JohnSL/3DR-Simple-Delta-Printer/STL/Spiral Bed Clamp Tall.STL

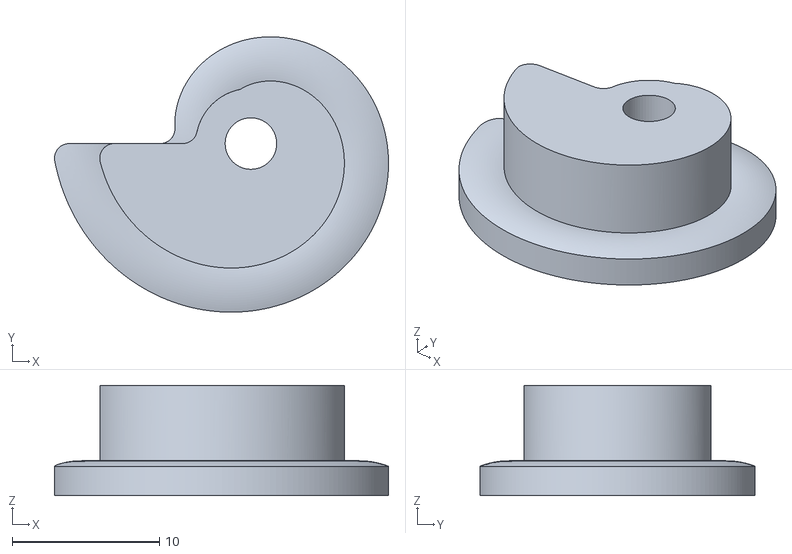
[picture p15: CAD file, 2014-05-10]
STL/Spiral Bed Clamp Tall.STL
22.7 x 18.7 x 7.50
