JohnSL/3DR-Simple-Delta-Printer/SolidWorks/FSR Platform.SLDPRT

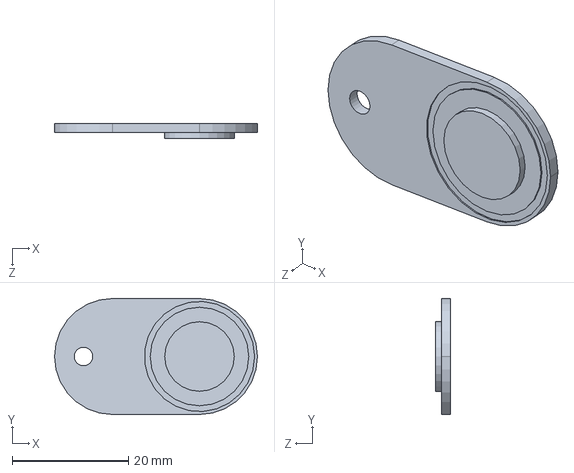
[picture p16: CAD file, 2014-05-10]
SolidWorks/FSR Platform.SLDPRT
35.0 x 20.0 x 2.50 mm
