JohnSL/3DR-Simple-Delta-Printer/STEP/Bearing Shaft Coupler.STEP

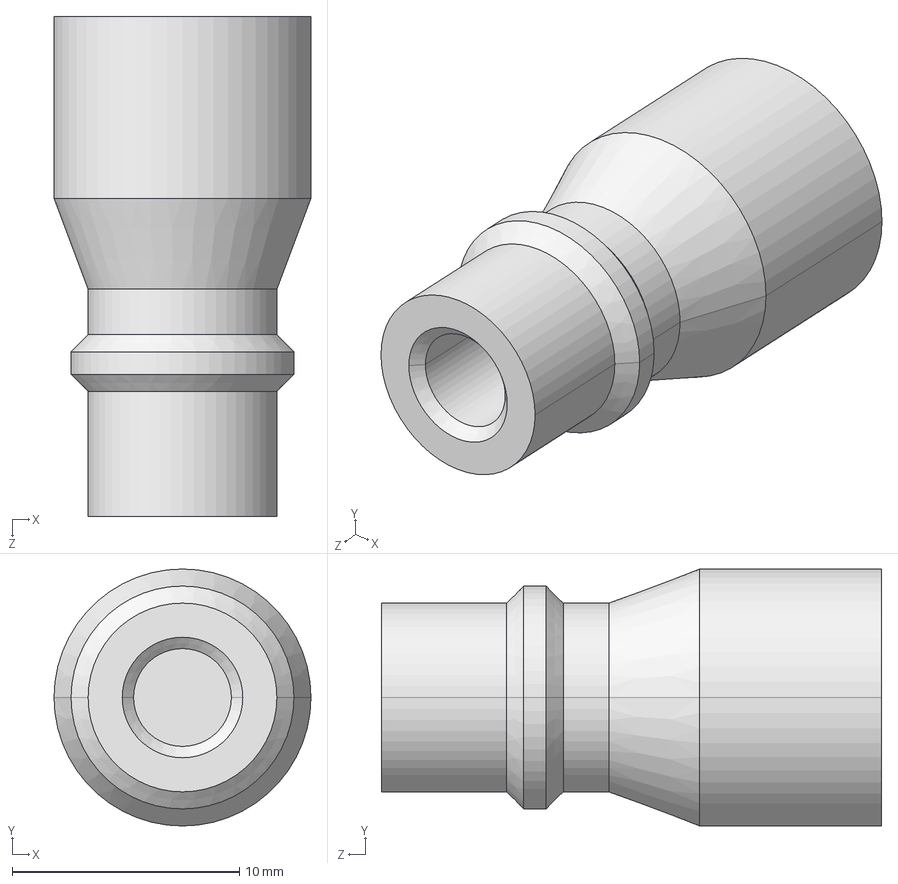
[picture p17: CAD file, 2014-02-23]
STEP/Bearing Shaft Coupler.STEP
11.3 x 11.3 x 22.0 mm
