JohnSL/3DR-Simple-Delta-Printer/STEP/Top/Wings.STEP

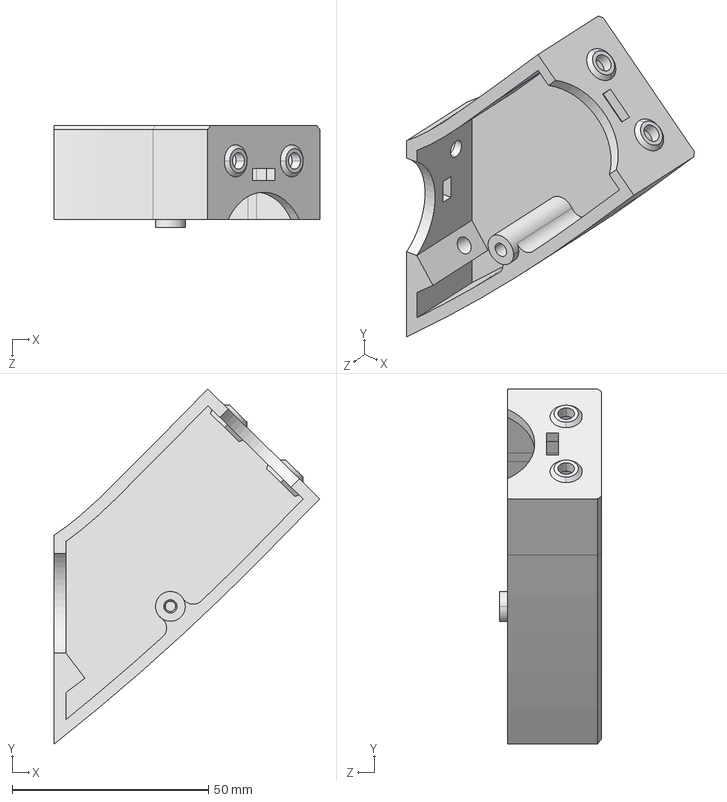
[picture p18: CAD file, 2014-03-03]
STEP/Top/Wings.STEP
67.7 x 90.5 x 26.0 mm
