JohnSL/3DR-Simple-Delta-Printer/STL/Simple Parts/Wings.STL

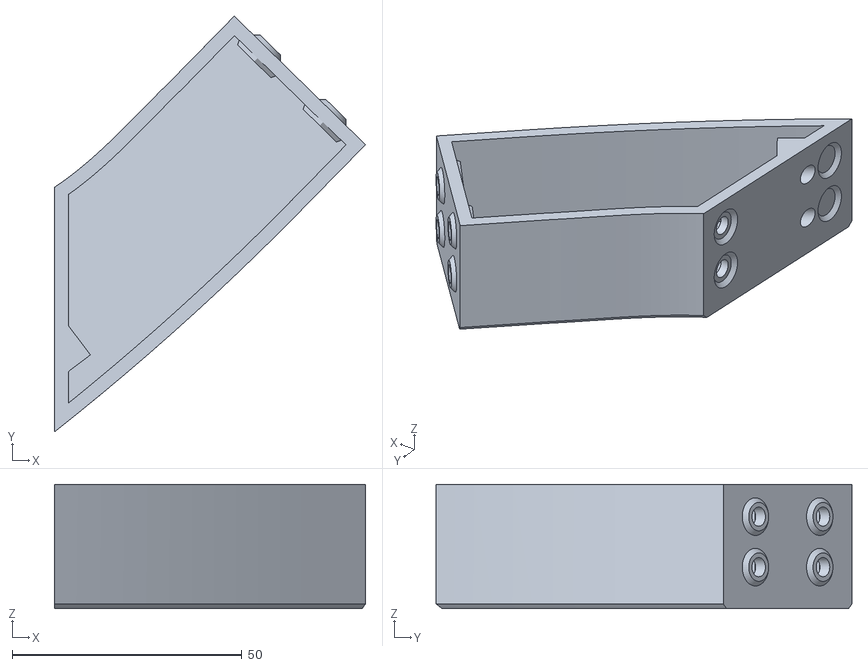
[picture p19: CAD file, 2013-11-02]
STL/Simple Parts/Wings.STL
67.7 x 90.5 x 27.0
