JohnSL/3DR-Simple-Delta-Printer/STEP/Carriage for LM8UU.STEP

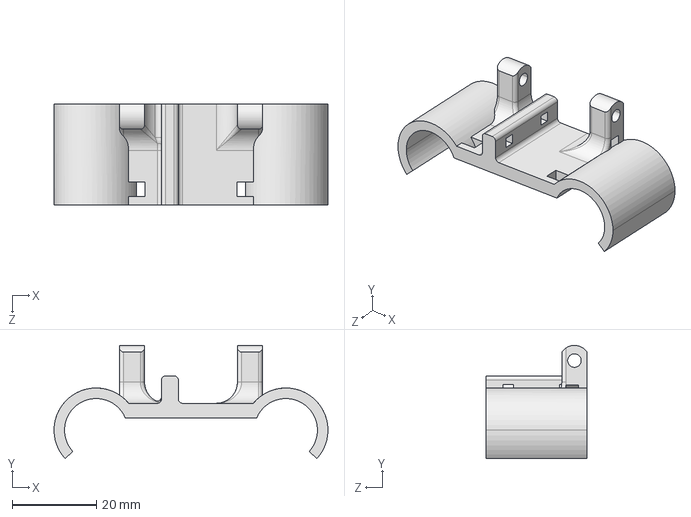
[picture p20: CAD file, 2014-02-23]
STEP/Carriage for LM8UU.STEP
65.0 x 26.9 x 24.0 mm
