JohnSL/3DR-Simple-Delta-Printer/STEP/Hot End/Hot End Holder Tabs.STEP

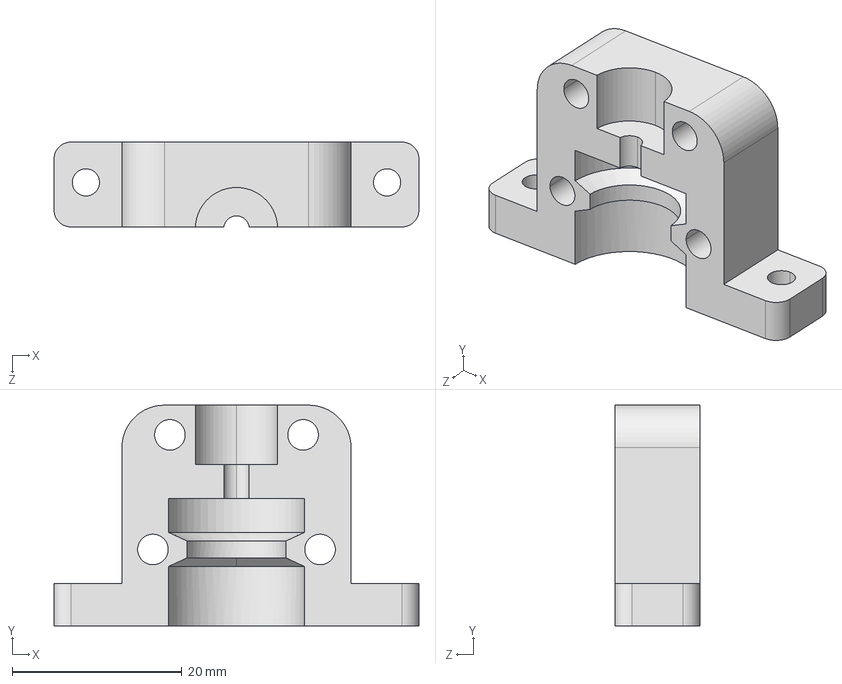
[picture p21: CAD file, 2014-02-23]
STEP/Hot End/Hot End Holder Tabs.STEP
43.0 x 26.0 x 10.0 mm
