JohnSL/3DR-Simple-Delta-Printer/STEP/Top/Wings with Power.STEP

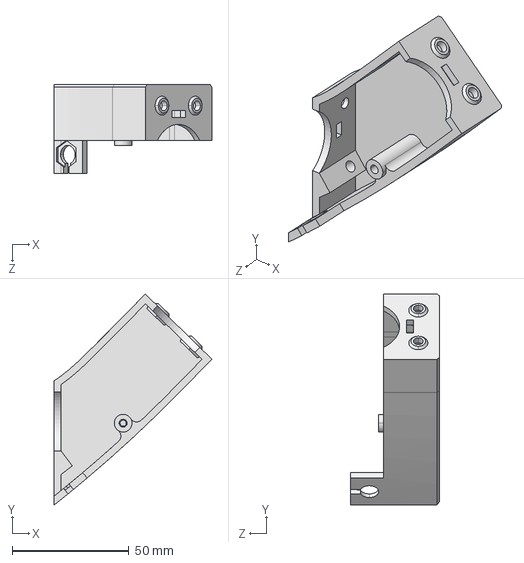
[picture p22: CAD file, 2014-03-03]
STEP/Top/Wings with Power.STEP
67.7 x 90.5 x 38.0 mm
