JohnSL/3DR-Simple-Delta-Printer/STL/2020extrusion_cap-nohole.stl

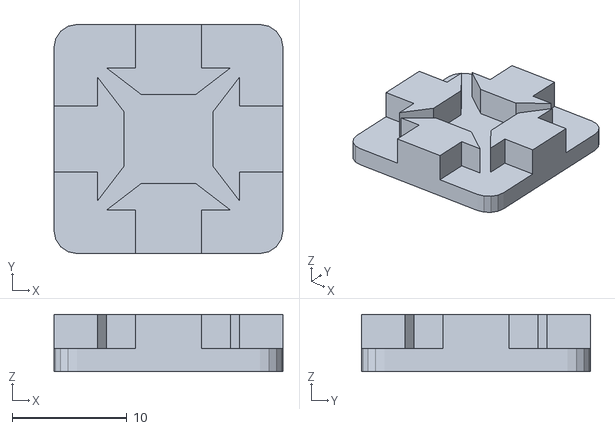
[picture p23: CAD file, 2013-11-30]
STL/2020extrusion_cap-nohole.stl
20.0 x 20.0 x 5.00
