JohnSL/3DR-Simple-Delta-Printer/STEP/Hot End/Hot End Plate.STEP

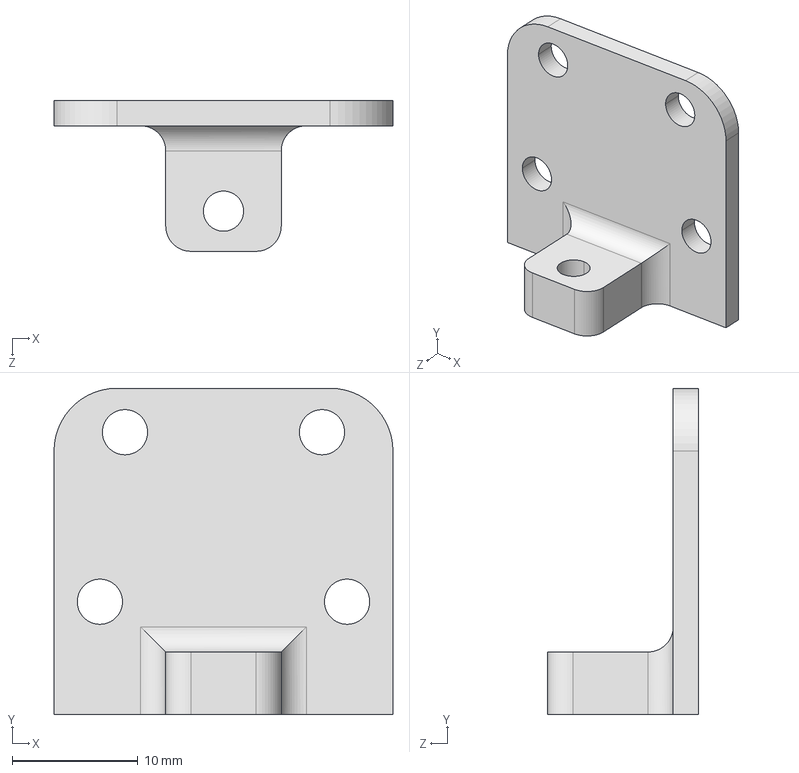
[picture p24: CAD file, 2014-02-23]
STEP/Hot End/Hot End Plate.STEP
27.0 x 26.0 x 12.0 mm
