JohnSL/3DR-Simple-Delta-Printer/STEP/Top/Wing Mirror Long Top.STEP

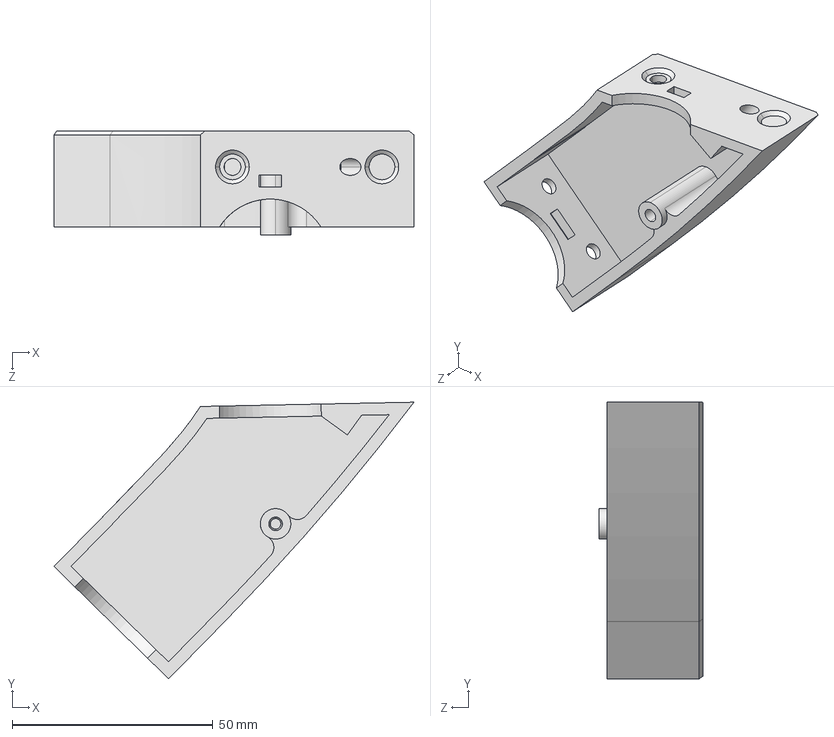
[picture p25: CAD file, 2014-03-03]
STEP/Top/Wing Mirror Long Top.STEP
89.7 x 69.0 x 26.0 mm
