JohnSL/3DR-Simple-Delta-Printer/STEP/Hot End/Fan and LED Mount.STEP

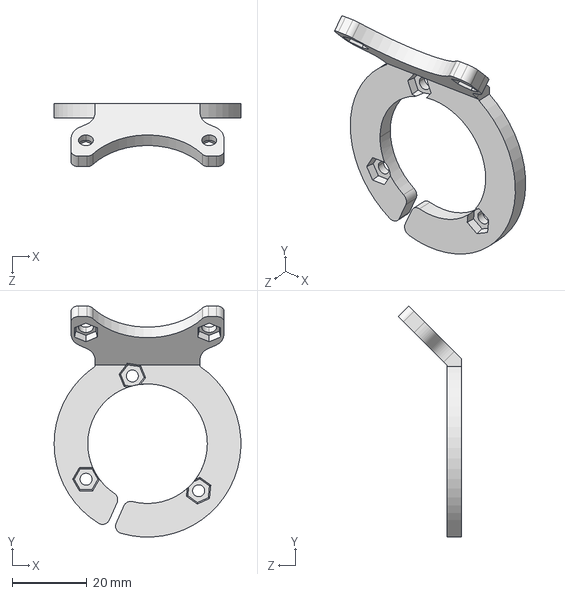
[picture p26: CAD file, 2014-02-23]
STEP/Hot End/Fan and LED Mount.STEP
50.0 x 61.8 x 17.0 mm
