JohnSL/3DR-Simple-Delta-Printer/STEP/Hot End/Platform.STEP

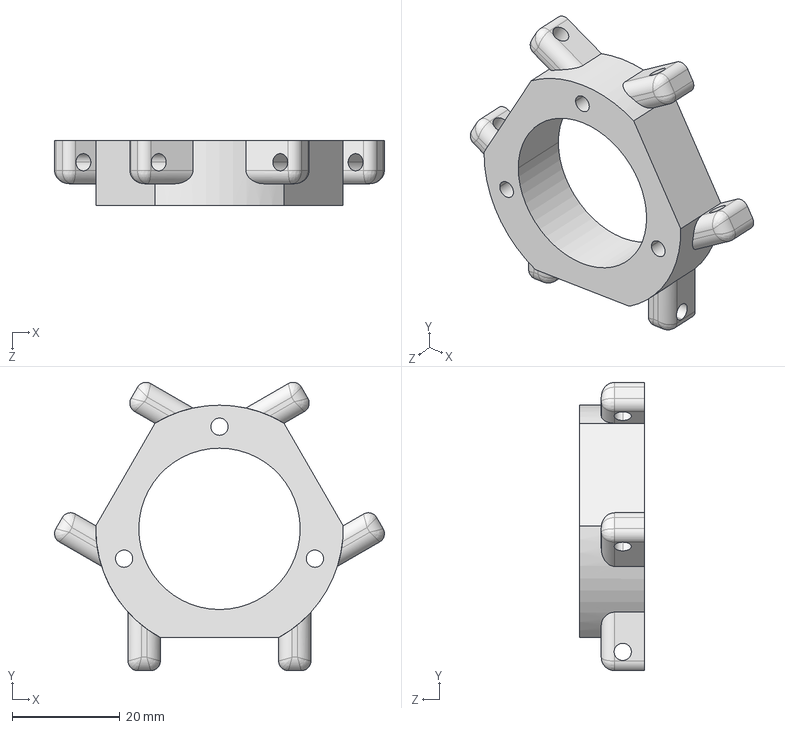
[picture p27: CAD file, 2014-02-23]
STEP/Hot End/Platform.STEP
61.4 x 53.6 x 12.0 mm
