JohnSL/3DR-Simple-Delta-Printer/SolidWorks/Rod Tensioner.SLDPRT

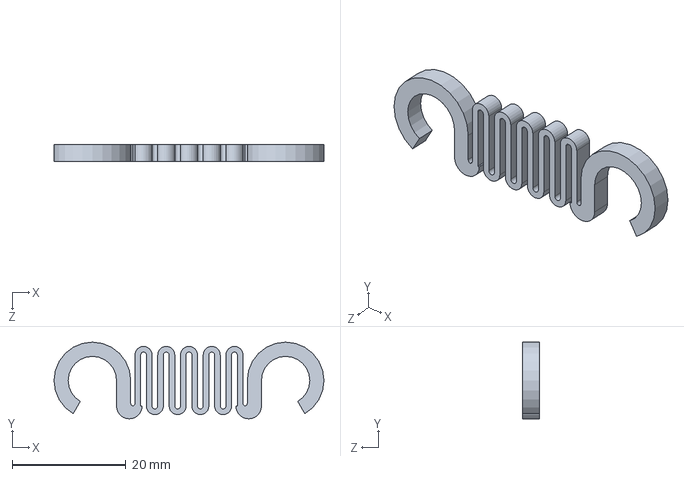
[picture p28: CAD file, 2014-01-16]
SolidWorks/Rod Tensioner.SLDPRT
47.5 x 13.5 x 3.00 mm
