JohnSL/3DR-Simple-Delta-Printer/SolidWorks/Acrylic Plate.SLDPRT

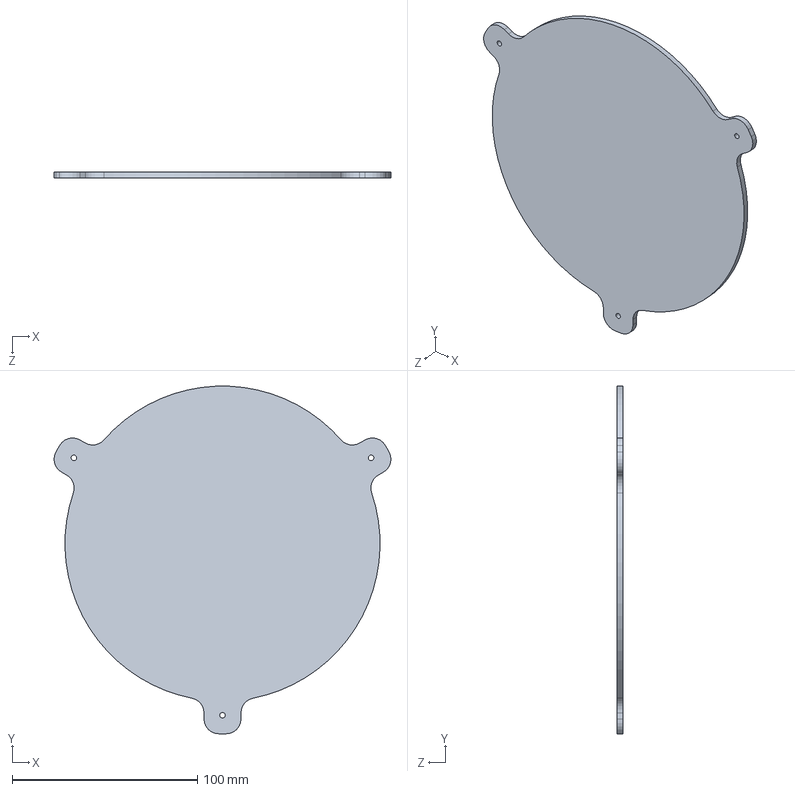
[picture p29: CAD file, 2013-11-30]
SolidWorks/Acrylic Plate.SLDPRT
181.8 x 187.5 x 3.17 mm
