JohnSL/3DR-Simple-Delta-Printer/SolidWorks/Round Plate.SLDPRT

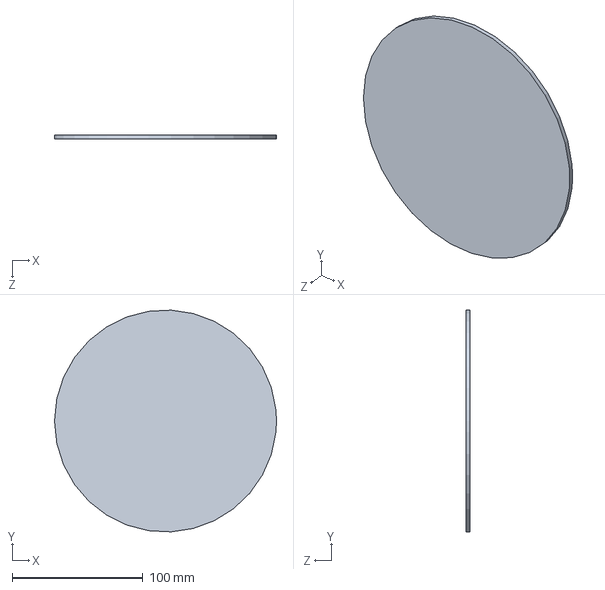
[picture p30: CAD file, 2013-11-30]
SolidWorks/Round Plate.SLDPRT
170.0 x 169.8 x 3.00 mm
