JohnSL/3DR-Simple-Delta-Printer/SolidWorks/Hot End.SLDPRT

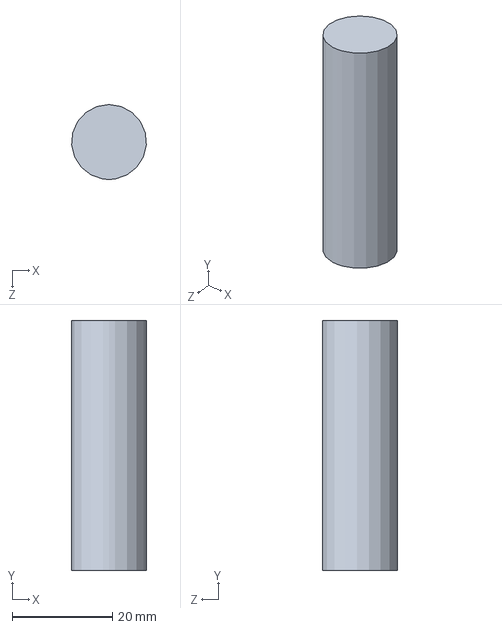
[picture p31: CAD file, 2013-11-30]
SolidWorks/Hot End.SLDPRT
14.9 x 50.0 x 15.0 mm
