JohnSL/3DR-Simple-Delta-Printer/SolidWorks/Fan.SLDPRT

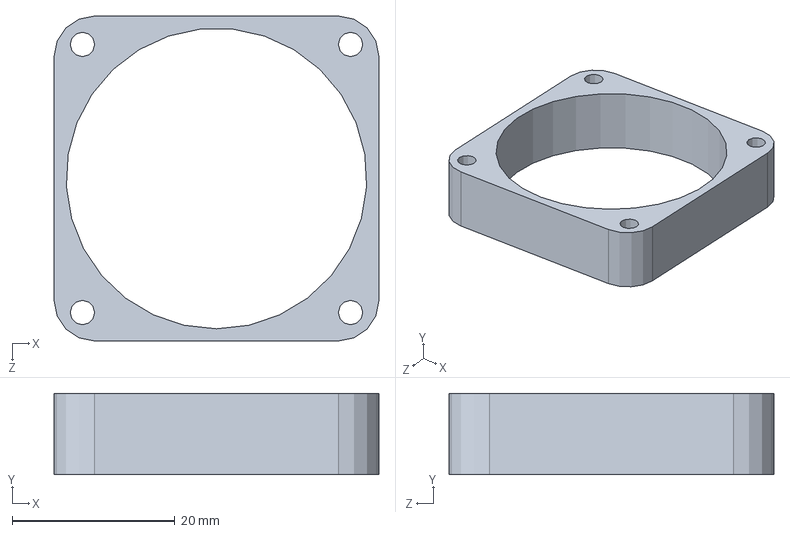
[picture p32: CAD file, 2013-11-30]
SolidWorks/Fan.SLDPRT
40.0 x 10.0 x 40.0 mm
