JohnSL/3DR-Simple-Delta-Printer/SolidWorks/Fan Side Mount.SLDPRT

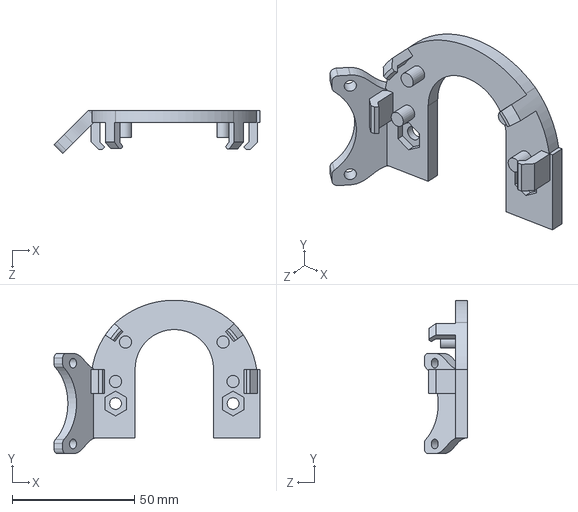
[picture p33: CAD file, 2013-11-30]
SolidWorks/Fan Side Mount.SLDPRT
84.1 x 62.7 x 17.7 mm
