JohnSL/3DR-Simple-Delta-Printer/SolidWorks/MirrorWings.SLDPRT

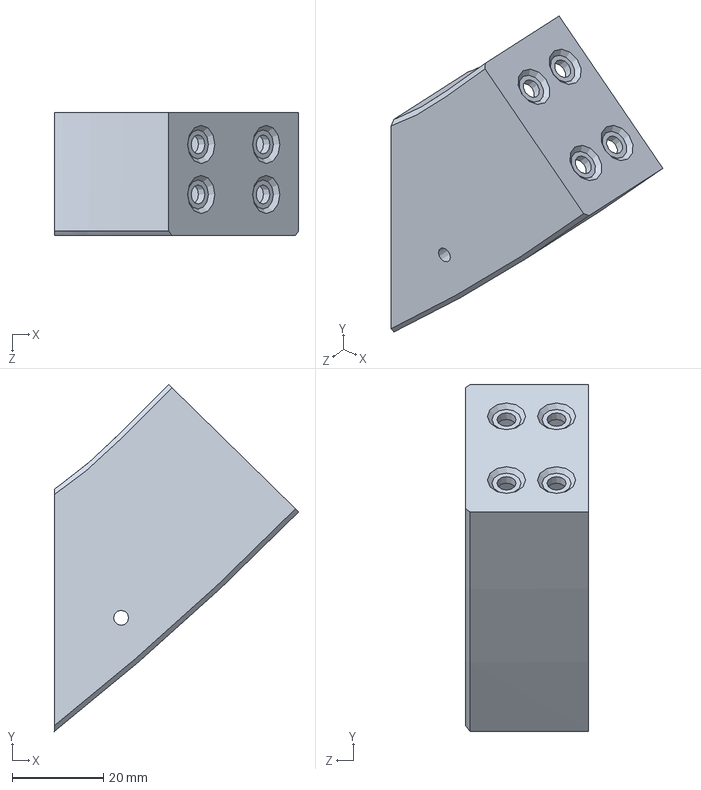
[picture p34: CAD file, 2013-11-07]
SolidWorks/MirrorWings.SLDPRT
53.7 x 76.2 x 27.0 mm
