JohnSL/3DR-Simple-Delta-Printer/SolidWorks/Spool.SLDPRT

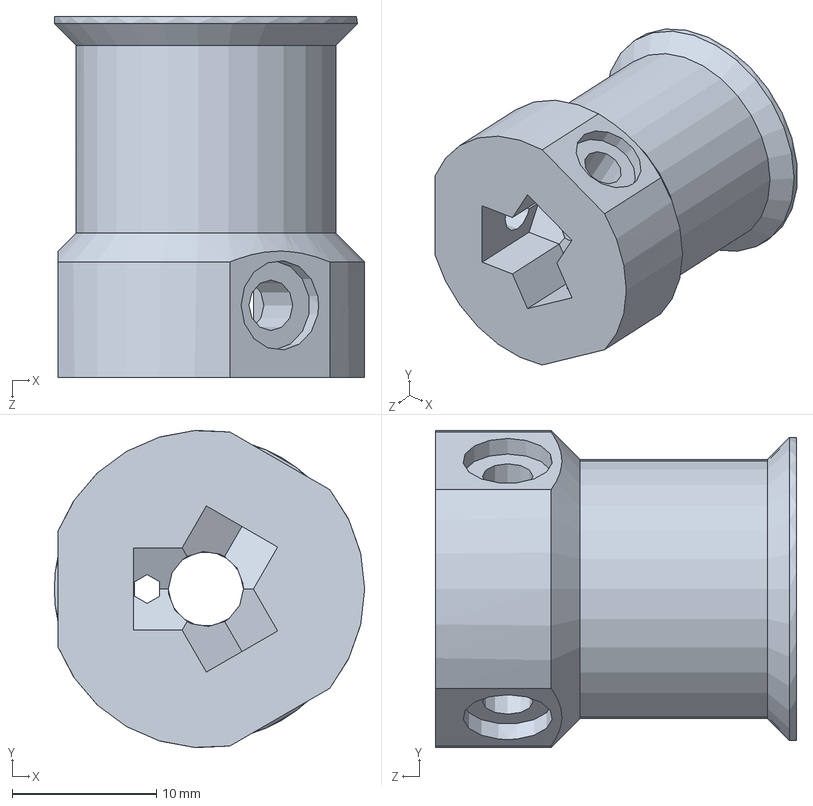
[picture p35: CAD file, 2013-11-07]
SolidWorks/Spool.SLDPRT
21.5 x 22.0 x 25.0 mm
