JohnSL/3DR-Simple-Delta-Printer/SolidWorks/Bed Holder.SLDPRT

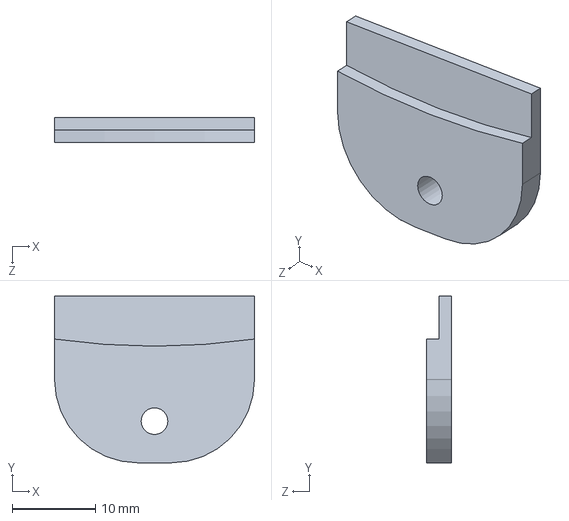
[picture p36: CAD file, 2013-10-21]
SolidWorks/Bed Holder.SLDPRT
24.0 x 20.0 x 3.00 mm
