JohnSL/3DR-Simple-Delta-Printer/SolidWorks/Wings.SLDPRT

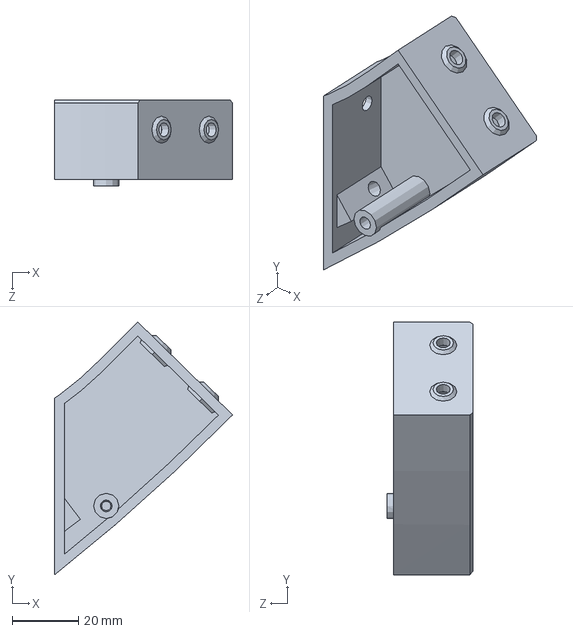
[picture p37: CAD file, 2013-10-21]
SolidWorks/Wings.SLDPRT
53.7 x 76.2 x 26.0 mm
