JohnSL/3DR-Simple-Delta-Printer/SolidWorks/3DR_Top_Electronics_Mount_V2_001_RTP.SLDPRT

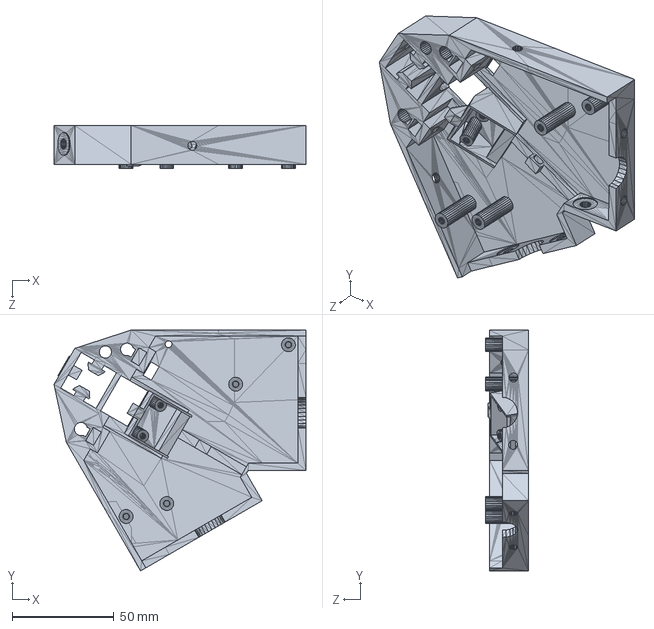
[picture p38: CAD file, 2013-10-16]
SolidWorks/3DR_Top_Electronics_Mount_V2_001_RTP.SLDPRT
123.7 x 118.2 x 21.2 mm
