JohnSL/3DR-Simple-Delta-Printer/SolidWorks/Printrboard.SLDPRT

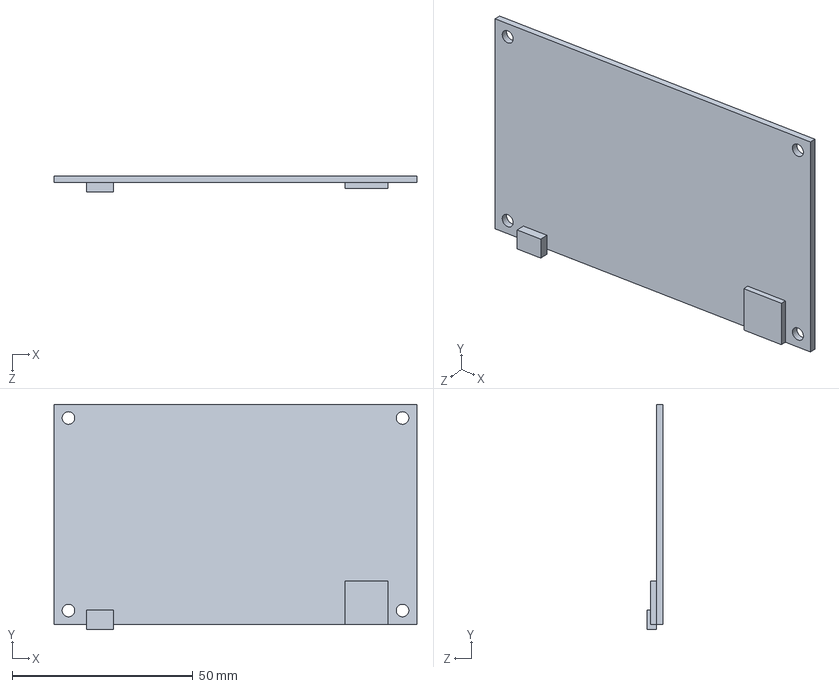
[picture p39: CAD file, 2013-10-16]
SolidWorks/Printrboard.SLDPRT
100.5 x 62.4 x 4.30 mm
