JohnSL/3DR-Simple-Delta-Printer/SolidWorks/M3 Button Head.SLDPRT

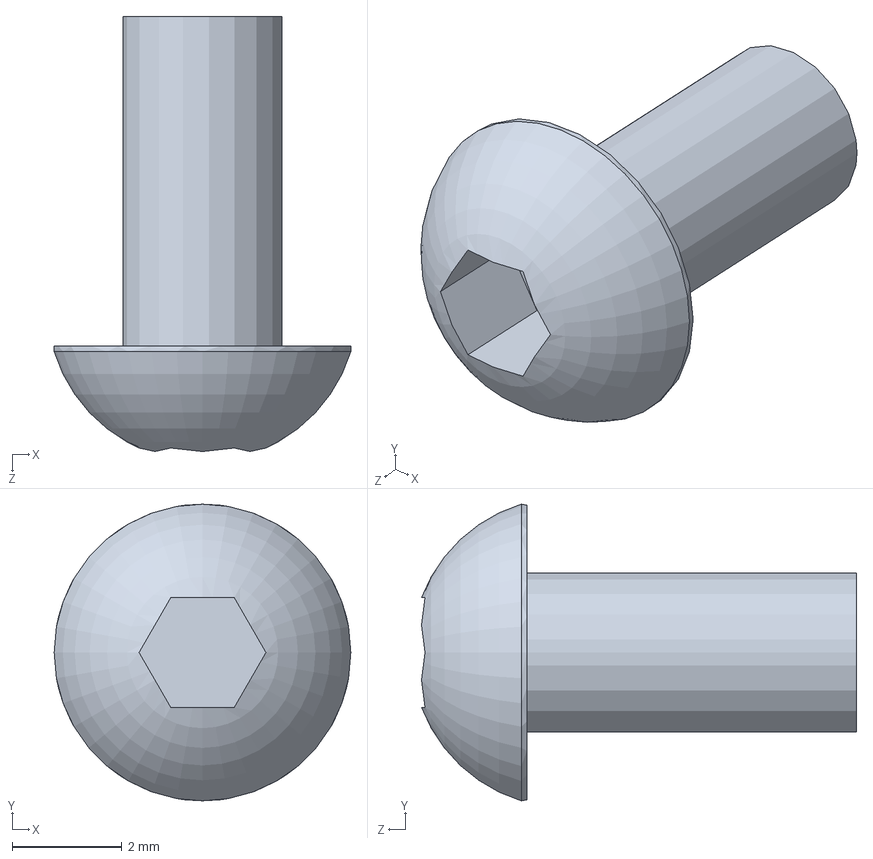
[picture p40: CAD file, 2013-10-16]
SolidWorks/M3 Button Head.SLDPRT
5.40 x 5.40 x 7.92 mm
