JohnSL/3DR-Simple-Delta-Printer/SolidWorks/3DR_Spool_V2_001_RTP.SLDPRT

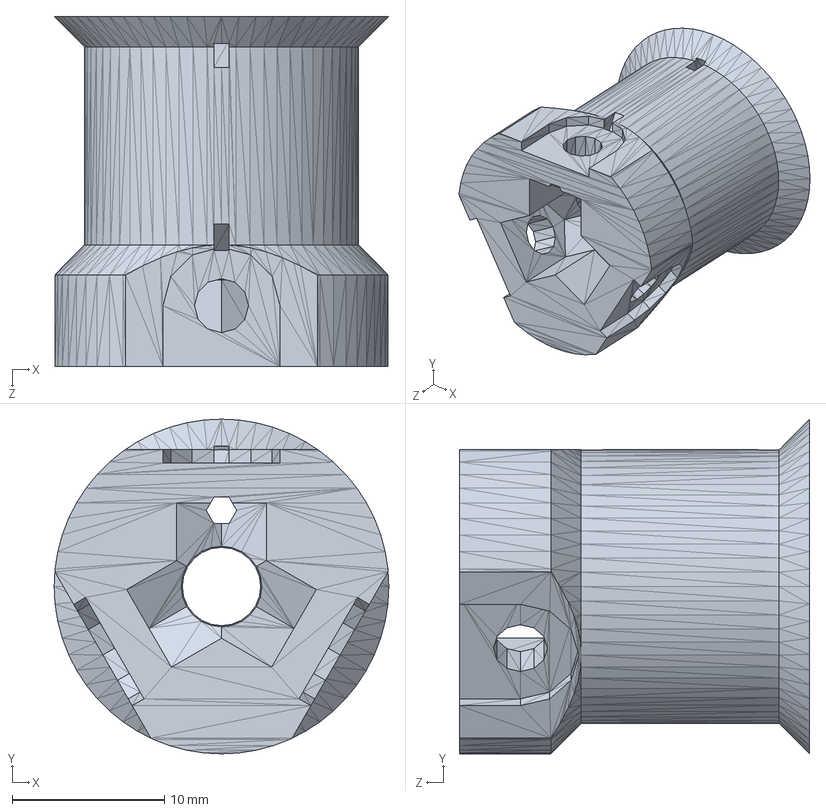
[picture p41: CAD file, 2013-10-16]
SolidWorks/3DR_Spool_V2_001_RTP.SLDPRT
22.0 x 22.0 x 23.0 mm
