JohnSL/3DR-Simple-Delta-Printer/SolidWorks/3DR_Carriage_V2_001_for_LM6UU_RTP.SLDPRT

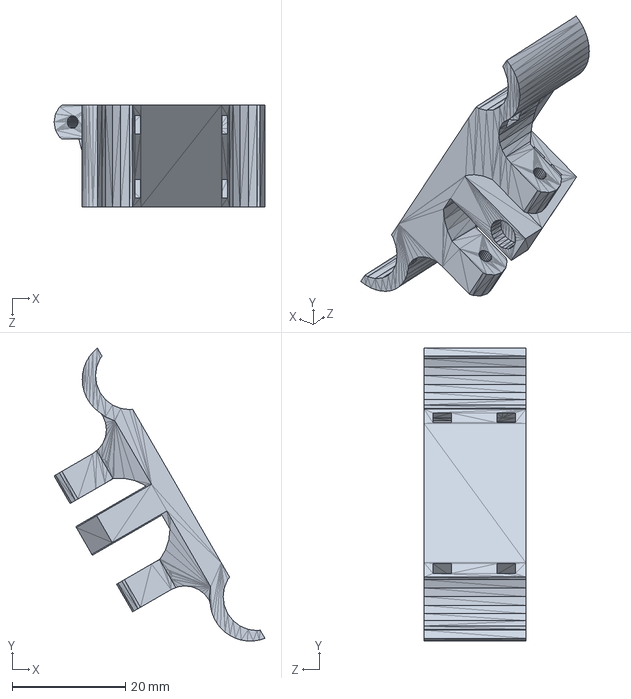
[picture p42: CAD file, 2013-10-16]
SolidWorks/3DR_Carriage_V2_001_for_LM6UU_RTP.SLDPRT
37.3 x 51.8 x 18.0 mm
