JohnSL/3DR-Simple-Delta-Printer/SolidWorks/3DR_Print_Bed_catch_V2_001_RTP.SLDPRT

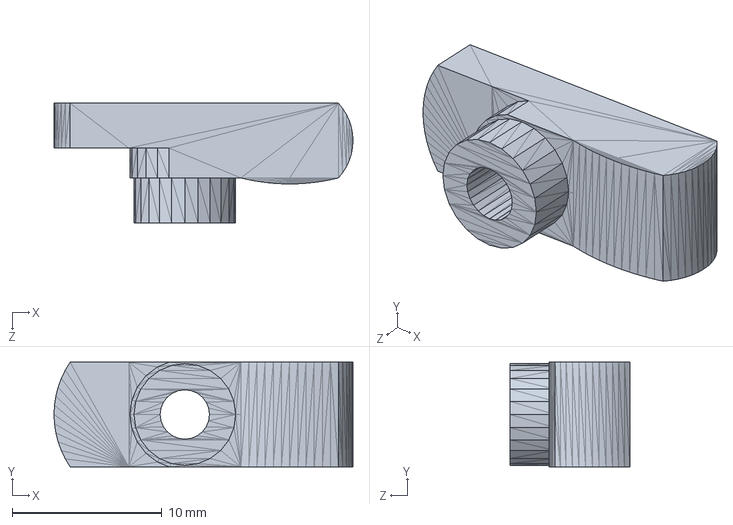
[picture p43: CAD file, 2013-10-16]
SolidWorks/3DR_Print_Bed_catch_V2_001_RTP.SLDPRT
20.0 x 7.00 x 8.00 mm
