JohnSL/3DR-Simple-Delta-Printer/SolidWorks/RGOCG8-400.SLDPRT

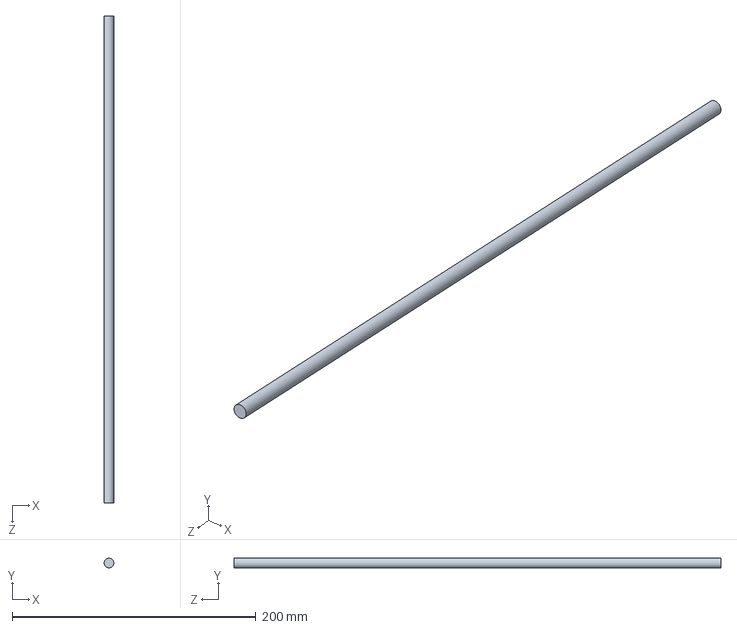
[picture p44: CAD file, 2013-10-16]
SolidWorks/RGOCG8-400.SLDPRT
8.00 x 8.00 x 400.0 mm
