JohnSL/3DR-Simple-Delta-Printer/SolidWorks/Carbon Rod.SLDPRT

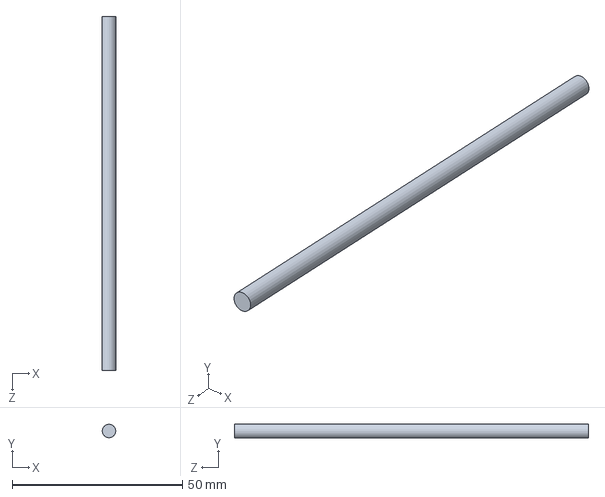
[picture p45: CAD file, 2013-10-16]
SolidWorks/Carbon Rod.SLDPRT
4.00 x 4.00 x 104.0 mm
