JohnSL/3DR-Simple-Delta-Printer/SolidWorks/3DR Bottom Center Foot.SLDPRT

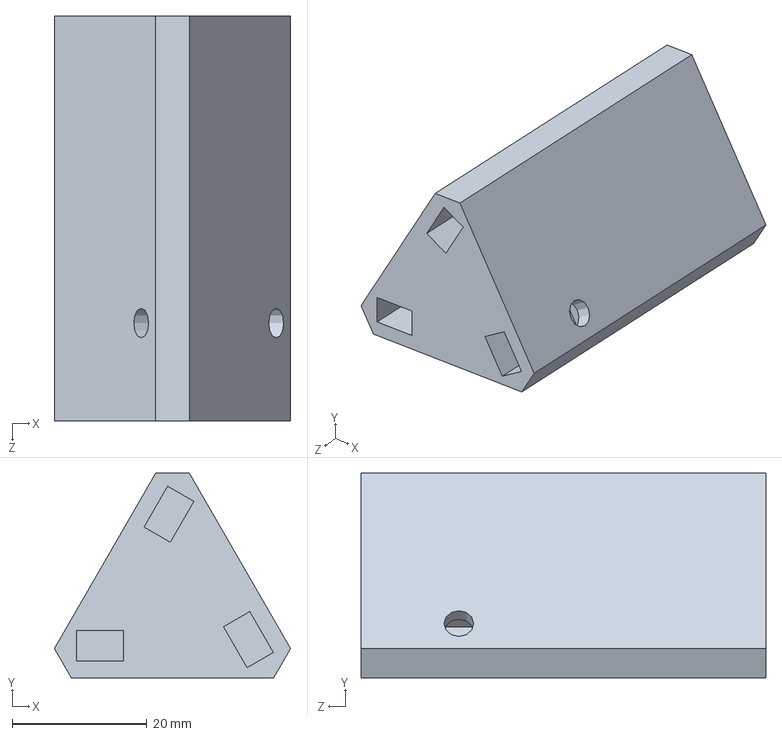
[picture p46: CAD file, 2013-10-16]
SolidWorks/3DR Bottom Center Foot.SLDPRT
35.0 x 30.3 x 60.0 mm
