JohnSL/3DR-Simple-Delta-Printer/SolidWorks/Thread.SLDPRT

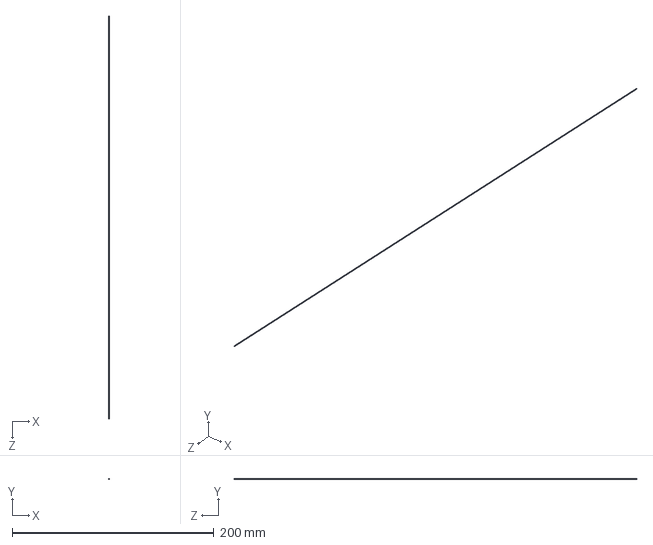
[picture p47: CAD file, 2013-10-16]
SolidWorks/Thread.SLDPRT
0.5 x 0.5 x 400.0 mm
