JohnSL/3DR-Simple-Delta-Printer/SolidWorks/Rod Ends.SLDPRT

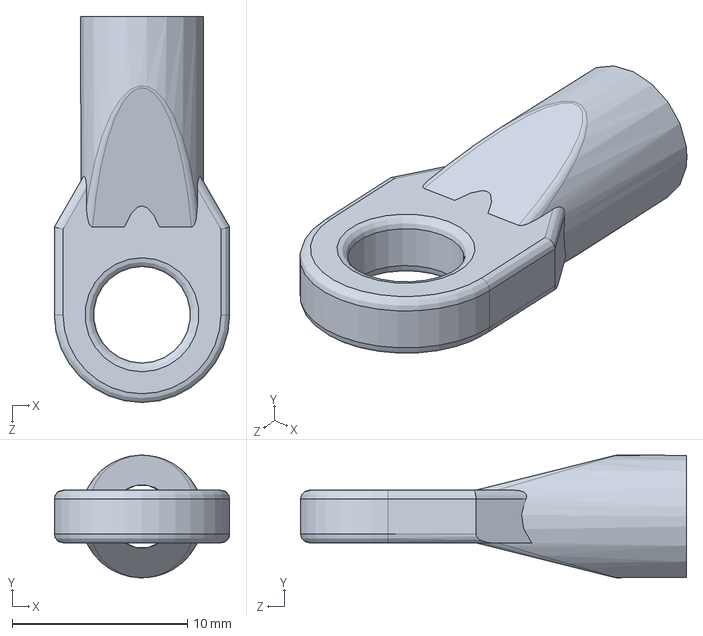
[picture p48: CAD file, 2013-10-16]
SolidWorks/Rod Ends.SLDPRT
10.0 x 6.99 x 22.0 mm
