JohnSL/3DR-Simple-Delta-Printer/SolidWorks/Carbon Rod Jig.SLDPRT

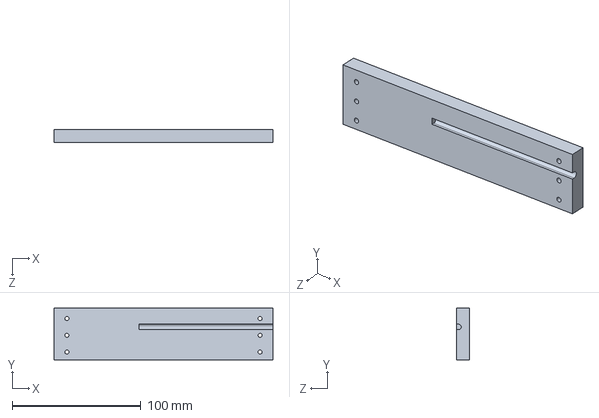
[picture p49: CAD file, 2013-10-16]
SolidWorks/Carbon Rod Jig.SLDPRT
170.0 x 40.0 x 10.0 mm
