JohnSL/3DR-Simple-Delta-Printer/SolidWorks/HFSB5-2020-450.sldprt

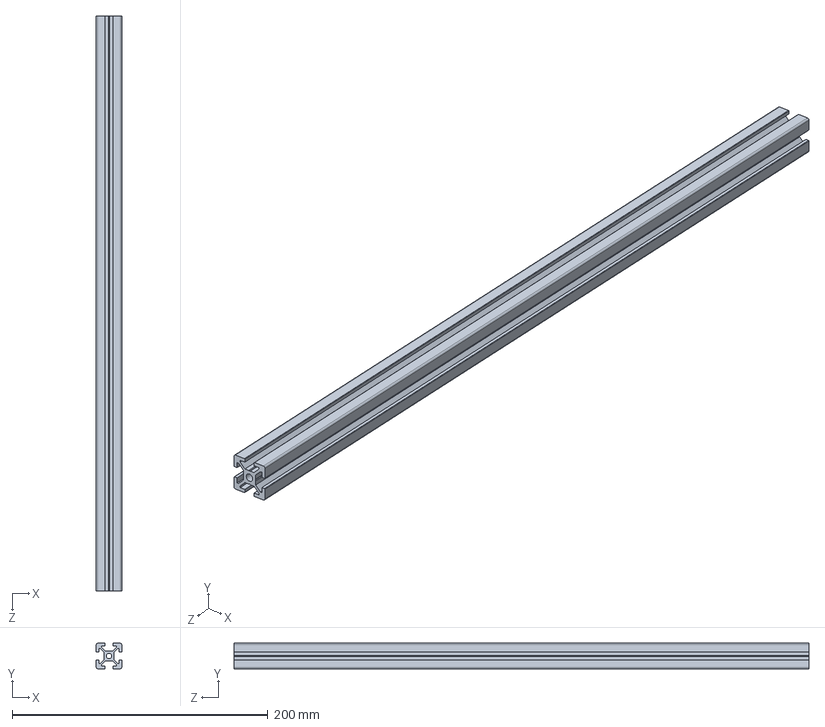
[picture p50: CAD file, 2013-10-16]
SolidWorks/HFSB5-2020-450.sldprt
20.0 x 20.0 x 450.0 mm
