JohnSL/3DR-Simple-Delta-Printer/SolidWorks/624ZZ.SLDPRT

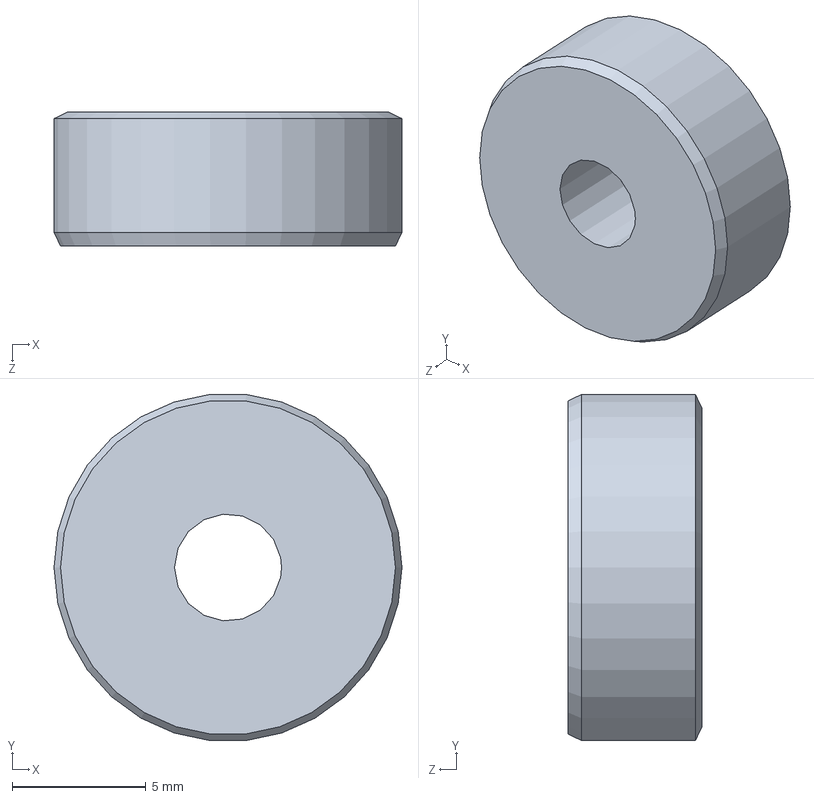
[picture p52: CAD file, 2013-10-16]
SolidWorks/624ZZ.SLDPRT
13.0 x 12.9 x 5.00 mm
