JohnSL/3DR-Simple-Delta-Printer/SolidWorks/Microswitch.SLDPRT

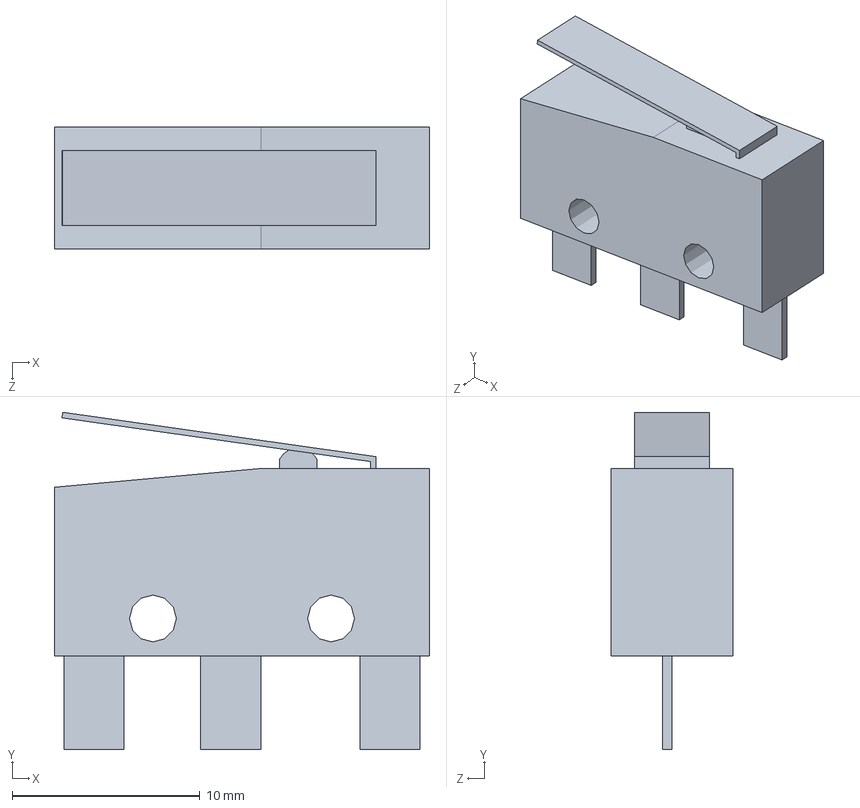
[picture p53: CAD file, 2013-10-16]
SolidWorks/Microswitch.SLDPRT
20.0 x 18.0 x 6.50 mm
